Hotakus/HellGateMonitor/ArtDesign/photoshop/clock/clock/clock_00.png

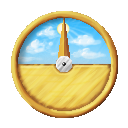
ArtDesign/photoshop/clock/clock/clock_00.png
