Hotakus/HellGateMonitor/ArtDesign/photoshop/clock/clock/clock_08.png

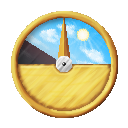
ArtDesign/photoshop/clock/clock/clock_08.png
