Hotakus/HellGateMonitor/ArtDesign/photoshop/clock/clock/clock_11.png

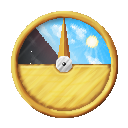
ArtDesign/photoshop/clock/clock/clock_11.png
