Hotakus/HellGateMonitor/ArtDesign/photoshop/clock/clock/clock_16.png

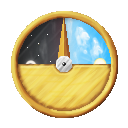
ArtDesign/photoshop/clock/clock/clock_16.png
