Hotakus/HellGateMonitor/ArtDesign/photoshop/clock/clock/clock_22.png

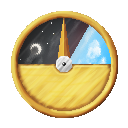
ArtDesign/photoshop/clock/clock/clock_22.png
