Hotakus/HellGateMonitor/ArtDesign/photoshop/clock/clock/clock_24.png

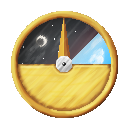
ArtDesign/photoshop/clock/clock/clock_24.png
