Hotakus/HellGateMonitor/ArtDesign/photoshop/clock/clock/clock_28.png

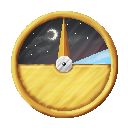
ArtDesign/photoshop/clock/clock/clock_28.png
