Hotakus/HellGateMonitor/ArtDesign/photoshop/clock/clock/clock_34.png

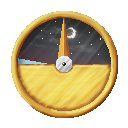
ArtDesign/photoshop/clock/clock/clock_34.png
