Hotakus/HellGateMonitor/ArtDesign/photoshop/clock/clock/clock_41.png

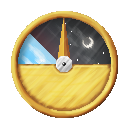
ArtDesign/photoshop/clock/clock/clock_41.png
