Hotakus/HellGateMonitor/ArtDesign/photoshop/clock/clock/clock_42.png

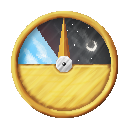
ArtDesign/photoshop/clock/clock/clock_42.png
