Hotakus/HellGateMonitor/ArtDesign/photoshop/clock/clock/clock_46.png

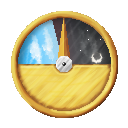
ArtDesign/photoshop/clock/clock/clock_46.png
