Hotakus/HellGateMonitor/ArtDesign/photoshop/clock/clock/clock_51.png

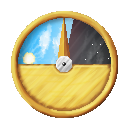
ArtDesign/photoshop/clock/clock/clock_51.png
