Hotakus/HellGateMonitor/ArtDesign/photoshop/clock/clock/clock_59.png

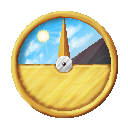
ArtDesign/photoshop/clock/clock/clock_59.png
