Hotakus/HellGateMonitor/ArtDesign/photoshop/HGM-assets/HGM.png

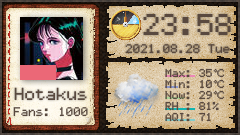
ArtDesign/photoshop/HGM-assets/HGM.png
