Hotakus/HellGateMonitor/ArtDesign/photoshop/TW/TW.png

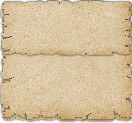
ArtDesign/photoshop/TW/TW.png
