Hotakus/HellGateMonitor/Datasheet/CA-C03.png

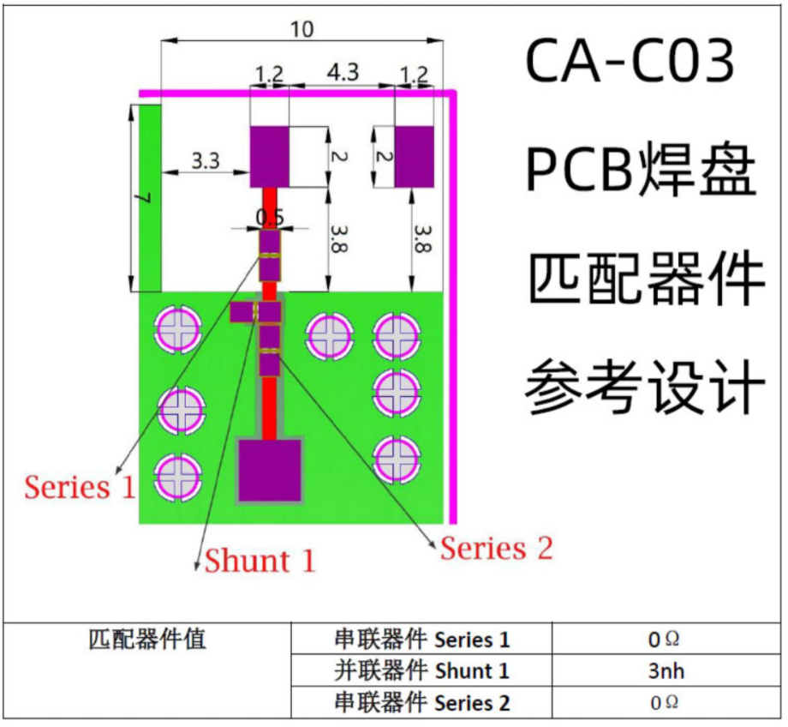
Datasheet/CA-C03.png
