Hotakus/HellGateMonitor/GuideImage/ArduinoConfig.png

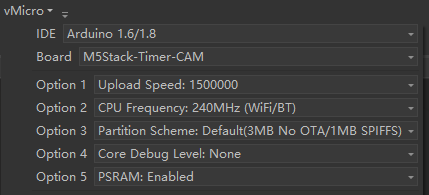
GuideImage/ArduinoConfig.png
