Hotakus/HellGateMonitor/GuideImage/Snipaste_2021-11-26_09-02-16.png

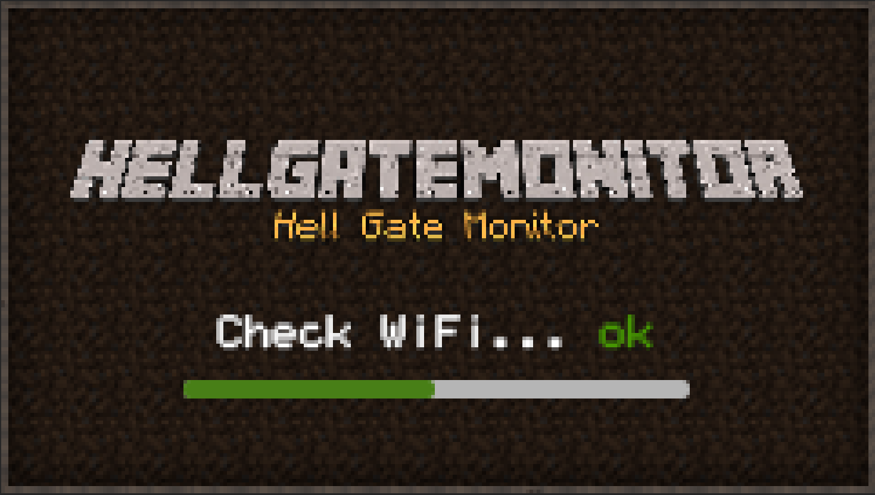
GuideImage/Snipaste_2021-11-26_09-02-16.png
