Hotakus/HellGateMonitor/GuideImage/SourceStruct.png

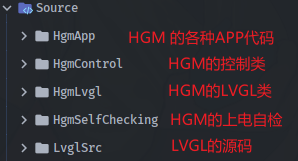
GuideImage/SourceStruct.png
