Hotakus/HellGateMonitor/Tools/hgm_spiffs/base_dir/sr_test.jpeg

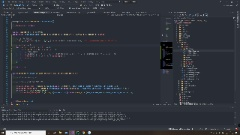
Tools/hgm_spiffs/base_dir/sr_test.jpeg
