Hotakus/HellGateMonitor/Source/HgmApp/BiliInfoRecv/BiliInfoRecv.h

/******************************************************************
 * @file BiliInfoRecv.h
 * @author Hotakus (...)
 * @email ttowfive@gmail.com
 * @brief ...
 * @version 1.0
 * @date 2021/8/15 16:33
 * @copyright Copyright (c) 2021/8/15
*******************************************************************/
#ifndef HELLGATEMONITOR_BILIINFORECV_H
#define HELLGATEMONITOR_BILIINFORECV_H

#include "../../HgmLvgl/HgmGUI/HgmFramework.h"
#include "../../HgmLvgl/HgmGUI/HgmTwView/HgmTwModel.h"

#include <Arduino.h>
#include <HTTPClient.h>

using namespace HgmGUI;

namespace HgmApplication {
#define BILI_CONFIG_FILE_PATH "/bilibili.json"
#define BILI_GET_GAP (10 * 60 * 1000)   // 10min

    class BiliInfoRecv
    {
    private:

    public:
        String basicInfoAPI = "http://api.bilibili.com/x/space/acc/info?mid=";
        String statAPI = "http://api.bilibili.com/x/relation/stat?vmid=";

        struct _info {
            String _uid = "";
            
            String userName = "";
            String userFaceImgUrl = "";
            uint8_t userLevel = 0;
            size_t userFans = 0;

            size_t userFaceImgBufSize = 0;
            uint8_t* userFaceImgBuf = NULL;   // default 64 x 64 jpg format
            uint16_t* userFaceBitmap = NULL;  // Bitmap that was decoded.
        } info;

        HgmTwModel::bili_dat_t bd;

        BiliInfoRecv();
        ~BiliInfoRecv();

        void initTask();
        void deInitTask();

        void begin();

        static void uid(String uid);
        static String uid();
        static bool Done();

        static uint8_t getLevel();
        static size_t getFollower();
        static String& getUserName();
        static void getBasicInfo();
        static int getUserFaceImg(uint16_t imgWidth = 64, uint16_t imgHeight = 64);
        static uint8_t* getUserFaceImgBuf(size_t* imgSize);
        static void* getUserFaceBitmap();
    };
};



#ifdef __cplusplus
extern "C" {
#endif

    /*...*/

#ifdef __cplusplus
}
#endif // __cplusplus

#endif //HELLGATEMONITOR_BILIINFORECV_H
