Hotakus/HellGateMonitor/Source/HgmLvgl/LvglPort/lv_port_disp.h

#ifndef LV_PORT_DISP_H
#define LV_PORT_DISP_H



#ifdef __cplusplus
extern "C" {
#endif

	
	void lv_port_disp_init(int16_t width, int16_t height, bool hwSwap);


#ifdef __cplusplus
} /*extern "C"*/
#endif

#endif /*LV_PORT_DISP_TEMPL_H*/
