Hotakus/HellGateMonitor/Source/HgmLvgl/LvglPort/lv_port_indev.h

/**
 * @file lv_port_indev_templ.h
 *
 */

 /*Copy this file as "lv_port_indev.h" and set this value to "1" to enable content*/
#if 1

#ifndef LV_PORT_INDEV_TEMPL_H
#define LV_PORT_INDEV_TEMPL_H

#ifdef __cplusplus
extern "C" {
#endif

void lv_port_indev_init(void);

#ifdef __cplusplus
} /*extern "C"*/
#endif

#endif /*LV_PORT_INDEV_TEMPL_H*/

#endif /*Disable/Enable content*/
