Hotakus/HellGateMonitor/resource.h

//{{NO_DEPENDENCIES}}
// Microsoft Visual C++ generated include file.
// Used by HellGateMonitor.rc

// 新对象的下一组默认值
// 
#ifdef APSTUDIO_INVOKED
#ifndef APSTUDIO_READONLY_SYMBOLS
#define _APS_NEXT_RESOURCE_VALUE        101
#define _APS_NEXT_COMMAND_VALUE         40001
#define _APS_NEXT_CONTROL_VALUE         1001
#define _APS_NEXT_SYMED_VALUE           101
#endif
#endif
