Hotakus/HellGateMonitor/Tools/util/SocketTest/SocketTest.ini

[UDP]
ServerPort=1024
SendToPort=4196
UDP_DEST_DOMAIN=192.168.1.200
Transimit_Protocol=1
GroupIP0=230
GroupIP1=90
GroupIP2=76
GroupIP3=1
Dynamic=0

[TCP]
ServerPort=8080
ClientPort=20
TCP_DEST_DOMAIN=192.168.174.234
ClientLocalPort=0

[System]
SendModeFile=0
RecvFileName=E:\temp\0N.txt
SendFileName=C:\Users\55307\Desktop\HardwareJsonPack.json
SendHex=0
RecvHex=0
WorkMode=1
CloseReport=0
TimeGap=2000
RecvBufSize=2000
RecvDataTimes=0
MiniRecvInterval=500
