Hotakus/HellGateMonitor/Source/HgmLvgl/HgmGUI/HgmTwView/HgmTwModel.cpp

#include "HgmTwModel.h"
#include "HgmTwView.h"

using namespace HgmGUI;

HgmGUI::HgmTwModel::HgmTwModel()
{
}

HgmGUI::HgmTwModel::~HgmTwModel()
{
}

void HgmGUI::HgmTwModel::begin()
{
}

void HgmGUI::HgmTwModel::end()
{
}

void setData(HgmTwModel::tw_data_t* _dat)
{
    

}

HgmTwModel::tw_data_t* HgmGUI::HgmTwModel::getData()
{
    return &this->dat;
}
